ole00/afterburner/design/adapter18cv8/adapter_peel_18cv8.cir

$ 1 0.0000049999999999999996 0.5999443210467817 57 5 50 5e-11
R 64 0 32 0 0 0 40 15.5 0 0 0.5
r 96 0 96 48 0 10000
r 96 96 96 144 0 20000
f 48 208 96 208 32 1.5 0.02
w 64 0 96 0 0
w 96 176 96 192 0
w 96 224 96 288 0
R -48 208 -112 208 0 0 40 5 0 0 0.5
s 16 208 -48 208 0 1 false
w 48 208 16 208 0
g 336 288 336 320 0 0
f 288 48 336 48 33 1.5 0.02
w 96 48 144 48 0
w 96 0 160 0 0
w 288 0 336 0 0
w 336 0 336 32 0
r 368 112 368 160 0 200
w 400 192 464 192 0
c 336 192 336 240 4 0.000001 0.000325532744089085 0.001 0.1
w 224 288 336 288 0
r 464 192 464 240 0 10000
r 464 240 464 288 0 20000
f 416 352 464 352 32 1.5 0.02
w 464 320 464 336 0
w 464 368 464 400 0
g 464 400 464 416 0 0
s 16 352 -48 352 0 1 false
w 464 288 464 320 0
w 16 352 416 352 0
f 576 240 640 240 33 1.5 0.02
w 464 240 512 240 0
w 640 192 640 224 0
w 640 256 640 272 0
w 640 352 640 400 0
r 640 256 640 352 0 10000
w 640 272 704 272 0
w 640 192 704 192 0
p 704 192 704 240 3 0 1 10000000
p 704 272 704 336 3 0 1 10000000
w 704 240 768 240 0
w 768 240 768 400 0
w 768 400 704 400 0
w 704 400 640 400 0
w 704 336 704 400 0
w 640 400 512 400 0
w 512 400 464 400 0
w 464 192 512 192 0
w 576 192 640 192 0
p 512 192 512 240 3 0 1 10000000
p 16 208 16 288 3 0 0 10000000
w 16 288 96 288 0
w 512 192 576 192 0
w 512 240 576 240 0
r 624 0 624 48 0 4700
r 624 48 624 96 0 20000
w 624 96 624 176 0
w 816 176 816 400 0
w 816 400 768 400 0
w 336 0 624 0 0
p 736 48 736 0 3 0 1 10000000
w 816 0 816 176 0
207 688 48 688 0 4 PVE
w 624 48 688 48 0
w 688 48 736 48 0
207 64 0 64 -32 4 VPP
207 704 272 736 272 4 ERA
207 704 192 752 192 4 PVP
207 16 352 16 320 4 ERA_VH2
207 16 208 16 176 4 CTL_PVP
w -48 208 -48 352 0
s 16 416 -48 416 0 1 false
d 80 416 144 416 2 1N5712
w 16 416 80 416 0
w -48 416 -48 352 0
207 144 416 208 416 4 ERA
207 16 416 16 384 4 PIN_ALE_ERA
w 736 0 816 0 0
w 624 176 816 176 0
f 528 144 576 144 32 1.5 0.02
w 624 48 576 48 0
w 576 48 576 128 0
w 576 160 576 176 0
w 576 176 624 176 0
207 528 144 480 144 4 PVE_VH1
s 16 464 -48 464 0 1 false
w -48 464 -48 416 0
w 16 464 128 464 0
207 128 464 176 464 4 PVE_VH1
w 160 0 288 0 0
w 144 48 288 48 0
w 336 192 400 192 0
w 336 240 336 288 0
f 176 224 224 224 32 1.5 0.02
w 224 192 224 208 0
w 224 240 224 288 0
w 176 224 144 224 0
w 96 144 96 176 0
r 224 192 336 192 0 1000
w 96 48 96 96 0
w 96 288 144 288 0
w 144 288 224 288 0
w 96 176 144 176 0
w 144 176 144 224 0
r 304 112 304 160 0 200
w 304 112 304 96 0
w 304 96 336 96 0
w 336 96 368 96 0
w 368 96 368 112 0
w 304 160 304 176 0
w 304 176 336 176 0
w 336 176 336 192 0
w 336 176 368 176 0
w 368 176 368 160 0
x 124 244 179 247 4 12 Vgs\s\q\s16V
x 379 128 407 131 4 12 0.5W
x 318 128 346 131 4 12 0.5W
x 263 212 291 215 4 12 0.5W
w 336 64 336 80 0
w 336 80 336 96 0
x 65 30 80 33 4 12 R2
x 593 30 608 33 4 12 R6
x 593 78 608 81 4 12 R7
x 523 130 539 133 4 12 Q2
x 65 123 80 126 4 12 R3
x 349 51 365 54 4 12 Q3
x 279 111 294 114 4 12 R4
x 385 110 400 113 4 12 R5
x 239 179 254 182 4 12 R8
x 105 208 121 211 4 12 Q1
x 314 239 329 242 4 12 C1
x 237 227 253 230 4 12 Q6
x 431 221 446 224 4 12 R9
x 426 267 448 270 4 12 R10
x 652 238 668 241 4 12 Q5
x 609 302 630 305 4 12 R11
x 472 355 488 358 4 12 Q4
x 104 400 119 403 4 12 D1
o 37 16 0 4098 0.00244140625 0.1 0 1 PVP
o 38 64 0 x281216 0.01953125 0.1 1 1 8 2 0 ERA
o 48 64 0 x281216 0.0006103515625 0.1 2 1 8 2 0 P\sGate
o 49 64 0 4098 5 0.1 3 1 CTL_PVP
